EkardNT/GymClock/programs.cpp

#include <NTPClient.h>
#include <AceTime.h>
#include "programs.h"
#include "common.h"
#include "sound.h"
#include "debug.h"

using namespace ace_routine;

extern NTPClient timeClient;

int currProgram = PROGRAM_INIT;

int currentProgram() {
    return currProgram;
}

void changeProgram(int newProgram) {
    currProgram = newProgram;
    suspendAll(newProgram);
    switch (newProgram) {
        case PROGRAM_INIT:
            Debug.println("Changing to PROGRAM_INIT");
            initProgram.reset();
            if (initProgram.isSuspended()) {
                initProgram.resume();
            }
            break;
        case PROGRAM_TEST:
            Debug.println("Changing to PROGRAM_TEST");
            testProgram.reset();
            if (testProgram.isSuspended()) {
                testProgram.resume();
            }
            break;
        case PROGRAM_CLOCK:
            Debug.println("Changing to PROGRAM_CLOCK");
            clockProgram.reset();
            if (clockProgram.isSuspended()) {
                clockProgram.resume();
            }
            break;
        case PROGRAM_COUNTDOWN:
            Debug.println("Changing to PROGRAM_COUNTDOWN");
            countdownProgram.reset();
            if (countdownProgram.isSuspended()) {
                countdownProgram.resume();
            }
            break;
        case PROGRAM_STOPWATCH:
            Debug.println("Changing to PROGRAM_STOPWATCH");
            stopwatchProgram.reset();
            if (stopwatchProgram.isSuspended()) {
                stopwatchProgram.resume();
            }
            break;
        case PROGRAM_SCORED_COUNTDOWN:
            Debug.println("Changing to PROGRAM_SCORED_COUNTDOWN");
            scoredCountdownProgram.reset();
            if (scoredCountdownProgram.isSuspended()) {
                scoredCountdownProgram.resume();
            }
            break;
        default:
            Debug.println("ERROR: cannot change to unknown program!");
    }
}

void suspendAll(int exceptProgram) {
    Debug.printf("Suspending all programs except %d\r\n", exceptProgram);
    if (exceptProgram != PROGRAM_INIT) {
        initProgram.suspend();
    }
    if (exceptProgram != PROGRAM_TEST) {
        testProgram.suspend();
    }
    if (exceptProgram != PROGRAM_CLOCK) {
        clockProgram.suspend();
    }
    if (exceptProgram != PROGRAM_COUNTDOWN) {
        countdownProgram.suspend();
    }
    if (exceptProgram != PROGRAM_STOPWATCH) {
        stopwatchProgram.suspend();
    }
    if (exceptProgram != PROGRAM_SCORED_COUNTDOWN) {
        scoredCountdownProgram.suspend();
    }
}

int TestProgram::runCoroutine() {
    COROUTINE_LOOP() {
        Debug.println("Test program showing TEST");
        for (int i = 0; i < NUM_DIGITS; i++) {
            updateDigit(i, ' ');
        }
        updateDigit(1, 'T');
        updateDigit(2, 'E');
        updateDigit(3, 'S');
        updateDigit(4, 'T');

        // TODO
        tone(tonePin, NOTE_C4, 500);
        COROUTINE_DELAY(750);
        tone(tonePin, NOTE_E4, 500);
        COROUTINE_DELAY(750);
        tone(tonePin, NOTE_G4, 500);
        COROUTINE_DELAY(1500);

        Debug.println("Test program showing 0-9");
        for (int i = 0; i < NUM_DIGITS; i++) {
            updateDigit(i, '0' + i);
        }

        COROUTINE_DELAY(2000);

        Debug.println("Test program showing all 8s");
        for (int i = 0; i < NUM_DIGITS; i++) {
            updateDigit(i, '8');
        }

        COROUTINE_DELAY(2000);
    }
}

int InitProgram::runCoroutine() {
    COROUTINE_BEGIN();
    Debug.println("Start of Init program");

    clearDisplay();
    updateDigit(0, 'H');
    updateDigit(1, 'E');
    updateDigit(2, 'L');
    updateDigit(3, 'L');
    updateDigit(4, 'O');

    COROUTINE_DELAY(3000);
    soundRoutine.playSound(SOUND_STARTUP);
    COROUTINE_DELAY(2000);

    if (!networkActive) {
        clearDisplay();
        updateDigit(0, 'N');
        updateDigit(1, 'O');
        updateDigit(3, 'N');
        updateDigit(4, 'E');
        updateDigit(5, 'T');
        Debug.println("Waiting until network active");
        COROUTINE_AWAIT(networkActive);
    }

    Debug.println("Net on in InitProgram");
    clearDisplay();
    updateDigit(0, 'N');
    updateDigit(1, 'E');
    updateDigit(2, 'T');
    updateDigit(4, 'O');
    updateDigit(5, 'N');
    COROUTINE_DELAY(3000);

    changeProgram(PROGRAM_CLOCK);

    Debug.println("End of Init program");
    COROUTINE_END();
}

int ClockProgram::runCoroutine() {
    COROUTINE_LOOP() {
        unsigned long unixEpochSeconds = timeClient.getEpochTime();
        ace_time::TimeZone localTz = zoneManager.createForZoneInfo(&ace_time::zonedb::kZoneAmerica_Los_Angeles);
        ace_time::ZonedDateTime localTime = ace_time::ZonedDateTime::forUnixSeconds(unixEpochSeconds, localTz);

        uint8_t hour = localTime.hour();

        if (hour > 12 && !this->format24) {
            hour -= 12;
        }

        clearDisplay();
        show2DigitNumber(hour, 0);
        show2DigitNumber(localTime.minute(), 2);
        show2DigitNumber(localTime.second(), 4);
        show2DigitNumber(localTime.month(), 6);
        show2DigitNumber(localTime.day(), 8);

        COROUTINE_DELAY(250);
    }
}

int CountdownProgram::runCoroutine() {
    COROUTINE_BEGIN();
    Debug.println("Start of Countdown program");

    // Do an initial countdown before the first set.
    while (this->readySeconds > 0) {
        clearDisplay();
        show2DigitNumber(this->readySeconds, 2);
        show2DigitNumber(this->sets, 6);

        // Also beep the last 3 seconds.
        if (this->readySeconds <= 3) {
            soundRoutine.playSound(SOUND_BEEP);
        }

        COROUTINE_DELAY(1000);
        this->readySeconds -= 1;
    }

    // Count down the sets.
    while (this->sets > 0) {
        Debug.printf("Starting set %d\r\n", this->sets);
        clearDisplay();
        updateDigit(0, 'S');
        updateDigit(1, 'T');
        updateDigit(2, 'A');
        updateDigit(3, 'R');
        updateDigit(4, 'T');
        soundRoutine.playSound(SOUND_START_SET);
        COROUTINE_DELAY(2000);

        this->startMillis = millis();
        this->ageMillis = 0;

        // Count down the set duration.
        while (this->ageMillis < this->setDurationMillis) {
            unsigned long remainingMillis = this->setDurationMillis - this->ageMillis;
            unsigned long hoursPart = remainingMillis / MILLIS_PER_HOUR;
            remainingMillis -= hoursPart * MILLIS_PER_HOUR;
            unsigned long minutesPart = remainingMillis / MILLIS_PER_MINUTE;
            remainingMillis -= minutesPart * MILLIS_PER_MINUTE;
            unsigned long secondsPart = remainingMillis / MILLIS_PER_SECOND;
            remainingMillis -= secondsPart * MILLIS_PER_SECOND;

            clearDisplay();
            show2DigitNumber(hoursPart, 0);
            show2DigitNumber(minutesPart, 2);
            show2DigitNumber(secondsPart, 4);
            show2DigitNumber(this->sets, 6);

            COROUTINE_DELAY(250);

            unsigned long now = millis();
            // Just make sure the clock never goes backwards. This could probably never happen
            // on a single-core machine anyways but can't hurt to guard against it.
            if (now < this->startMillis) {
                now = this->startMillis;
            }
            this->ageMillis = now - this->startMillis;
        }

        this->sets -= 1;

        // Now enter the rest mode. Show "REST" on the display, flashing on and off on
        // one-second intervals. The remaining rest time is shown in the lower right digit
        // pair.
        if (this->sets > 0 && this->restSeconds > 0) {
            Debug.println("Entering rest period");
            soundRoutine.playSound(SOUND_START_REST);

            // TODO: play sound too
            static unsigned long remainingRestSeconds = this->restSeconds;
            while (remainingRestSeconds > 0) {
                clearDisplay();
                updateDigit(1, 'R');
                updateDigit(2, 'E');
                updateDigit(3, 'S');
                updateDigit(4, 'T');
                show2DigitNumber(this->sets, 6);
                show2DigitNumber(remainingRestSeconds, 8);

                remainingRestSeconds -= 1;
                COROUTINE_DELAY(1000);
            }
        }
    }

    Debug.println("Flashing done for Countdown");
    static int doneCounter;
    for (doneCounter = 0; doneCounter < 5; doneCounter++) {
        clearDisplay();
        updateDigit(1, 'D');
        updateDigit(2, 'O');
        updateDigit(3, 'N');
        updateDigit(4, 'E');
        show2DigitNumber(0, 6);

        COROUTINE_DELAY(1000);
        clearDisplay();
        show2DigitNumber(0, 6);
        COROUTINE_DELAY(750);
    }

    changeProgram(PROGRAM_CLOCK);

    Debug.println("End of Countdown program");
    COROUTINE_END();
}

int StopwatchProgram::runCoroutine() {
    COROUTINE_BEGIN();
    Debug.println("Start of Stopwatch program");

    clearDisplay();

    unsigned long now = millis();
    this->startMillis = now;
    this->lastBeepTimeMillis = now;

    while (true) {
        now = millis();
        unsigned long age = now > this->startMillis ? now - this->startMillis : 0;
        unsigned long hoursPart = age / MILLIS_PER_HOUR;
        age -= hoursPart * MILLIS_PER_HOUR;
        unsigned long minutesPart = age / MILLIS_PER_MINUTE;
        age -= minutesPart * MILLIS_PER_MINUTE;
        unsigned long secondsPart = age / MILLIS_PER_SECOND;
        age -= secondsPart * MILLIS_PER_SECOND;
        unsigned long decisecondsPart = age / 10;

        // Loop around once we exceed 99 hours.
        if (hoursPart > 99) {
            this->startMillis = millis();
            Debug.println("Stopwatch looped");
            continue;
        }

        // beepIntervalMillis == 0 disables the beep functionality.
        if (this->beepIntervalMillis > 0) {
            unsigned long millisSinceLastBeep = now > this->lastBeepTimeMillis ? now - this->lastBeepTimeMillis : 0;
            if (millisSinceLastBeep > this->beepIntervalMillis) {
                soundRoutine.playSound(SOUND_BEEP);
                this->lastBeepTimeMillis = now;
            }
        }

        // If the stopwatch has recorded over an hour, then show HH:MM:SS, otherwise show
        // MM:SS:DS.
        if (hoursPart > 0) {
            show2DigitNumber(hoursPart, 0);
            show2DigitNumber(minutesPart, 2);
            show2DigitNumber(secondsPart, 4);
            COROUTINE_DELAY(250);
        } else {
            show2DigitNumber(minutesPart, 0);
            show2DigitNumber(secondsPart, 2);
            show2DigitNumber(decisecondsPart, 4);
            COROUTINE_DELAY(75);
        }
    }

    Debug.println("End of Stopwatch program");
    COROUTINE_END();
}

int ScoredCountdownProgram::runCoroutine() {
    COROUTINE_BEGIN();
    Debug.println("Start of ScoredCountdown program");

    // Do an initial preparation countdown before the main loop.
    while (this->readySeconds > 0) {
        clearDisplay();
        show2DigitNumber(this->readySeconds, 2);
        show2DigitNumber(this->leftScore, 6);
        show2DigitNumber(this->rightScore, 8);

        // Also beep the last 3 seconds.
        if (this->readySeconds <= 3) {
            soundRoutine.playSound(SOUND_BEEP);
        }

        COROUTINE_DELAY(1000);
        this->readySeconds -= 1;
    }

    soundRoutine.playSound(SOUND_START_SET);

    this->startMillis = millis();
    this->ageMillis = 0;

    // Count down the duration.
    while (this->ageMillis < this->durationMillis) {
        unsigned long remainingMillis = this->durationMillis - this->ageMillis;
        unsigned long hoursPart = remainingMillis / MILLIS_PER_HOUR;
        remainingMillis -= hoursPart * MILLIS_PER_HOUR;
        unsigned long minutesPart = remainingMillis / MILLIS_PER_MINUTE;
        remainingMillis -= minutesPart * MILLIS_PER_MINUTE;
        unsigned long secondsPart = remainingMillis / MILLIS_PER_SECOND;
        remainingMillis -= secondsPart * MILLIS_PER_SECOND;
        unsigned long decisecondsPart = remainingMillis / 10;

        clearDisplay();
        if (hoursPart > 0) {
            show2DigitNumber(hoursPart, 0);
            show2DigitNumber(minutesPart, 2);
            show2DigitNumber(secondsPart, 4);
            show2DigitNumber(this->leftScore, 6);
            show2DigitNumber(this->rightScore, 8);
            COROUTINE_DELAY(250);
        } else {
            show2DigitNumber(minutesPart, 0);
            show2DigitNumber(secondsPart, 2);
            show2DigitNumber(decisecondsPart, 4);
            show2DigitNumber(this->leftScore, 6);
            show2DigitNumber(this->rightScore, 8);
            COROUTINE_DELAY(75);
        }

        unsigned long now = millis();
        // Just make sure the clock never goes backwards. This could probably never happen
        // on a single-core machine anyways but can't hurt to guard against it.
        if (now < this->startMillis) {
            now = this->startMillis;
        }
        this->ageMillis = now - this->startMillis;
    }

    Debug.println("Flashing done for ScoredCountdown");
    static int doneCounter;
    for (doneCounter = 0; doneCounter < 5; doneCounter++) {
        clearDisplay();
        updateDigit(1, 'D');
        updateDigit(2, 'O');
        updateDigit(3, 'N');
        updateDigit(4, 'E');
        show2DigitNumber(0, 6);

        COROUTINE_DELAY(1000);
        clearDisplay();
        show2DigitNumber(0, 6);
        COROUTINE_DELAY(750);
    }

    changeProgram(PROGRAM_CLOCK);

    Debug.println("End of ScoredCountdown program");
    COROUTINE_END();
}
